Juanvmont/Poncho-EDU-CIAA-NXP-RF-2.4GHz-Antena-PCB/Trx_antena_pcb/doc/edu-ciaa-nxp_pinout_a4_v4r0_es.pdf

# ASIGNACIÓN DE PINES

# Pernia

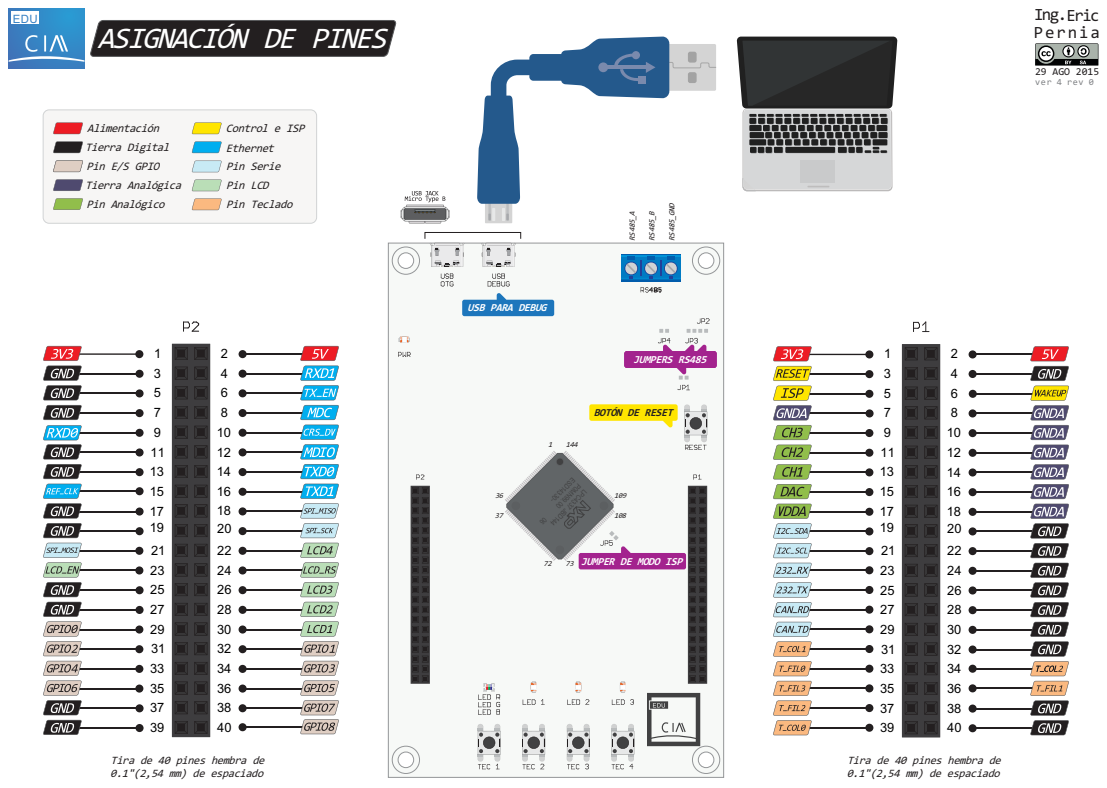
[picture p4: page 1]
Alimentación; Tierra Digital; Pin Analógico; Tierra Analógica; Pin E/S GPIO; Pin Serie; Control e ISP; Pin LCD; Pin Teclado; Ethernet; EDU; LPC4337 JBD144; ESD14330-; JUMPER DE MODO ISP; 29 AGO 2015 ver 4 rev 0; Ing.Eric; JUMPERS RS485; RS485_GND

USB PARA DEBUG

BOTÓN DE RESET

Tira de 40 pines hembra de
0.1"(2,54 mm) de espaciado

# PINES UTILIZADOS DEL NXP LPC4337 JBD144

# Pernia

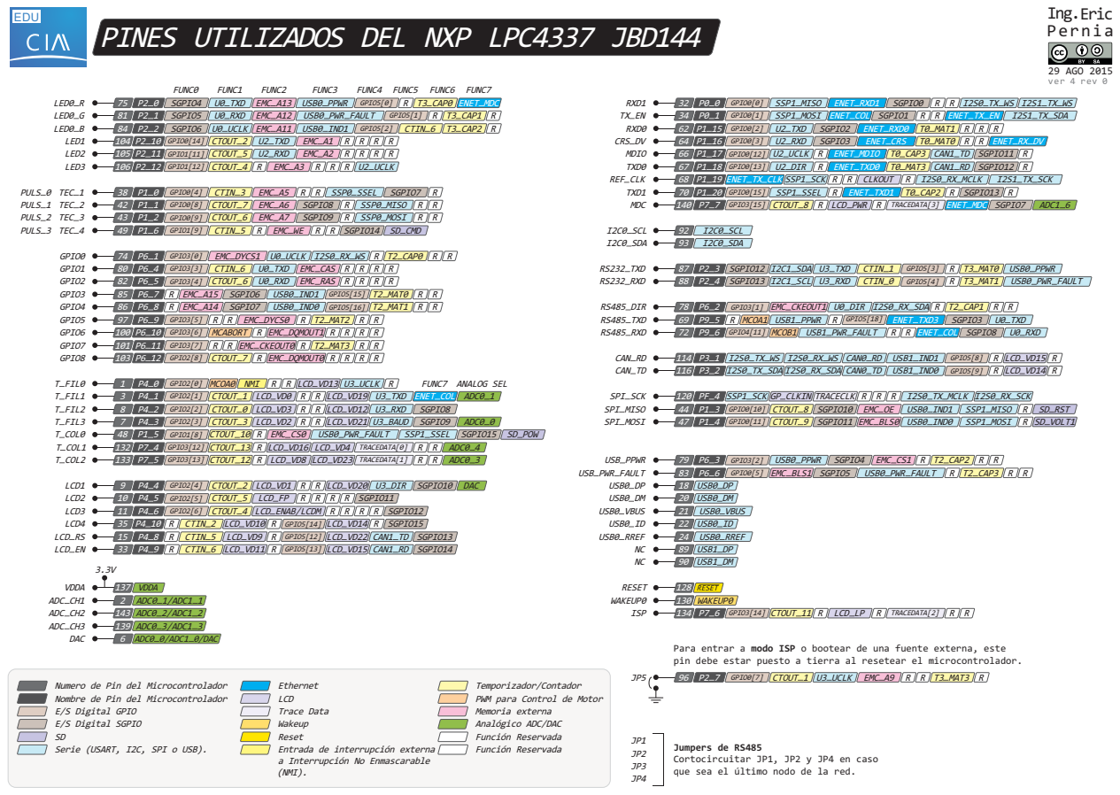
[picture p5: page 2]

Para entrar a modo ISP o bootear de una fuente externa, este
pin debe estar puesto a tierra al resetear el microcontrolador.

Numero de Pin del Microcontrolador
Nombre de Pin del Microcontrolador
E/S Digital GPIO
E/S Digital SGPIO
Serie (USART, I2C, SPI o USB).

Temporizador/Contador
PWM para Control de Motor
Memoria externa
Analógico ADC/DAC
Función Reservada

Jumpers de RS485
Cortocircuitar JP1, JP2 y JP4 en caso
que sea el último nodo de la red.
